sinara-hw/RFSOC-AMC/DOC/front-top.png

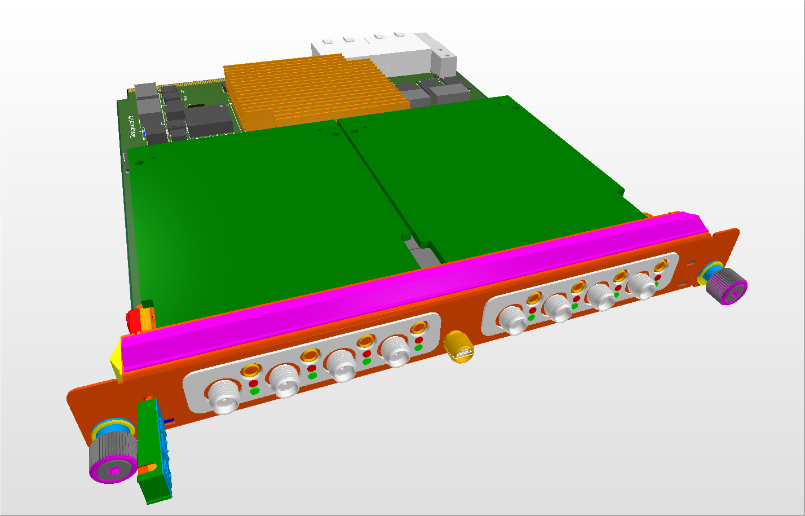
DOC/front-top.png
